BrandonBNguyen/Pitot-Static-Tube-Project/CAD/Teensy LC Model/Teensy_lc v8.png

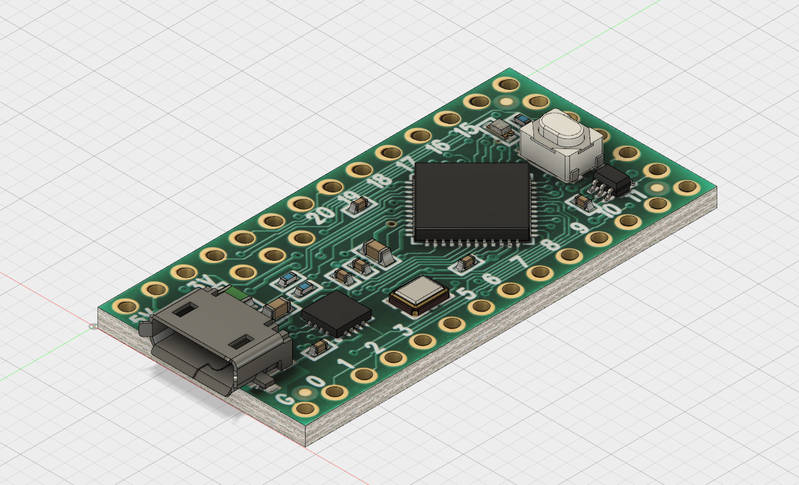
CAD/Teensy LC Model/Teensy_lc v8.png
