BrandonBNguyen/Pitot-Static-Tube-Project/CAD/Arduino Uno R3 Model/603 resistor.SLDPRT

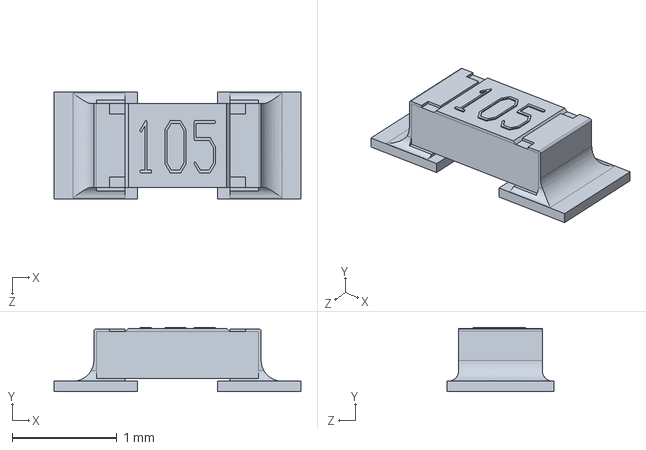
[picture p31: CAD file, 2021-01-14]
CAD/Arduino Uno R3 Model/603 resistor.SLDPRT
2.36 x 0.615 x 1.02 mm
