BrandonBNguyen/Pitot-Static-Tube-Project/CAD/Version 1/Pressure Sensor Housing.SLDPRT

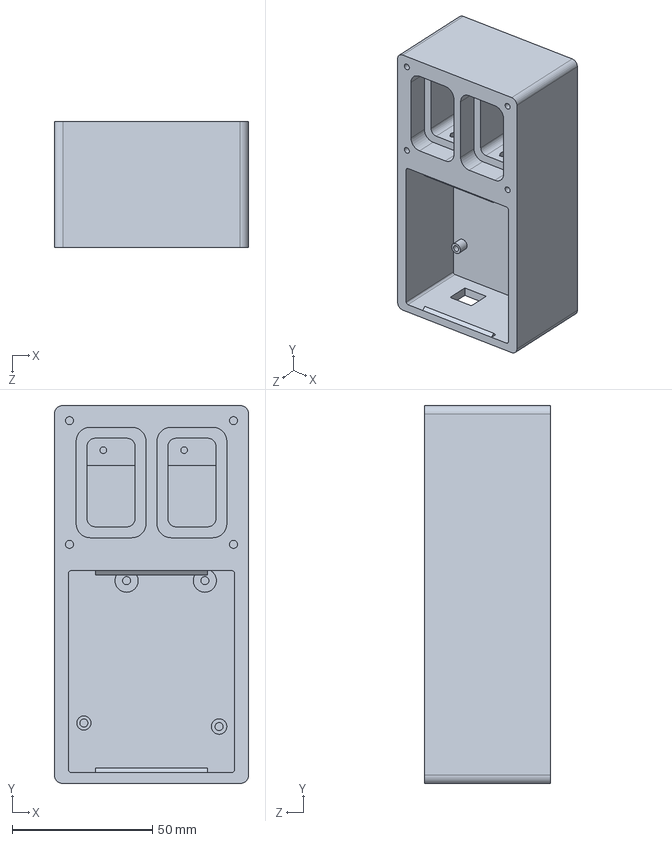
[picture p32: CAD file, 2021-02-09]
CAD/Version 1/Pressure Sensor Housing.SLDPRT
69.3 x 134.9 x 45.0 mm
