BrandonBNguyen/Pitot-Static-Tube-Project/Print STL Files/Pressure Sensor Housing Lid.STL

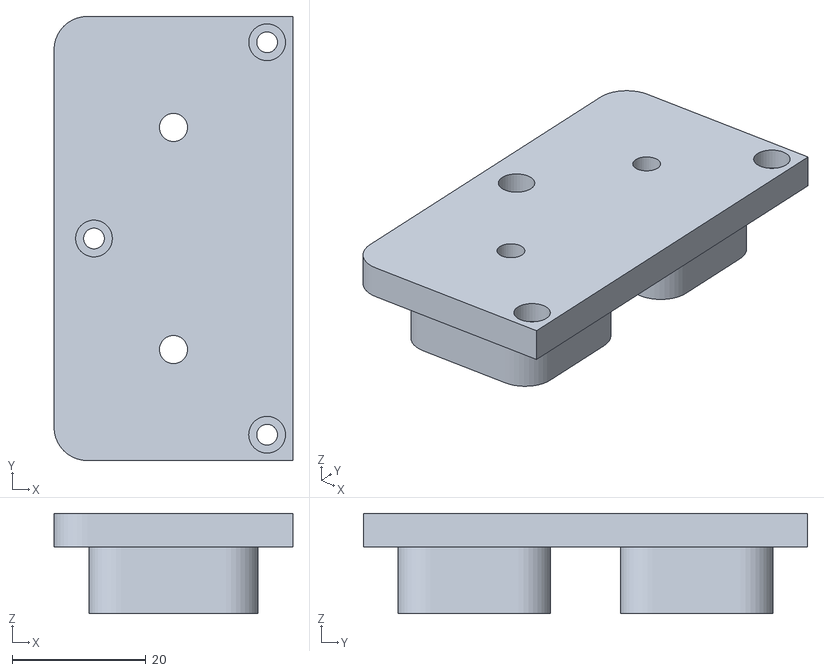
[picture p33: CAD file, 2021-02-09]
Print STL Files/Pressure Sensor Housing Lid.STL
35.7 x 66.4 x 15.0
