BrandonBNguyen/Pitot-Static-Tube-Project/Test Prints/Teensy LC Lid.STL

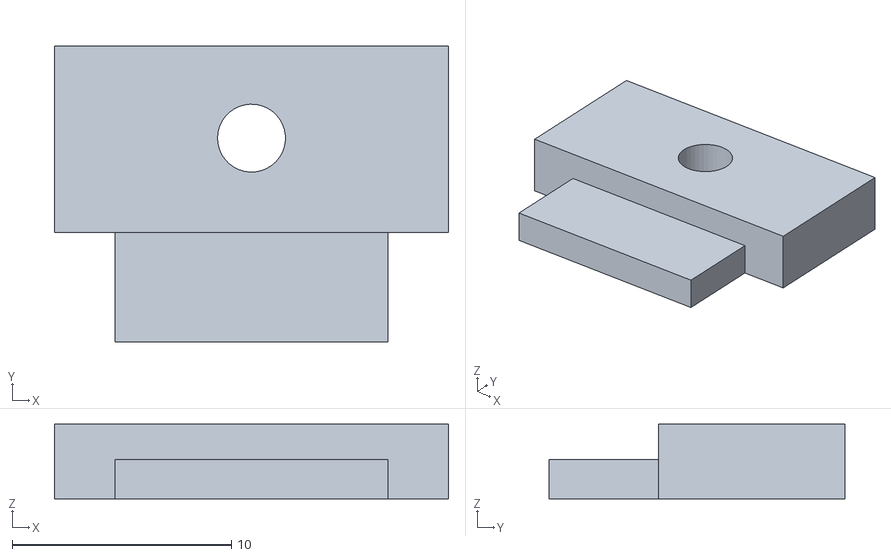
[picture p34: CAD file, 2021-02-09]
Test Prints/Teensy LC Lid.STL
18.0 x 13.5 x 3.40
