BrandonBNguyen/Pitot-Static-Tube-Project/CAD/Arduino Uno R3 Model/2pin_header__02.sldprt

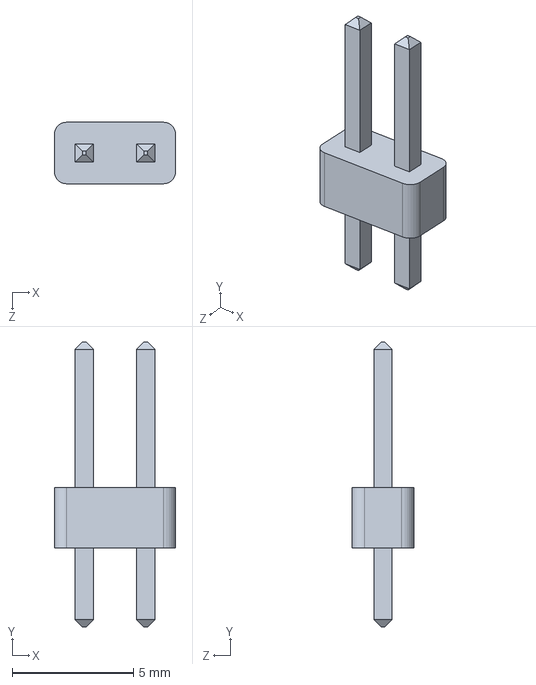
[picture p35: CAD file, 2021-01-14]
CAD/Arduino Uno R3 Model/2pin_header__02.sldprt
5.00 x 11.8 x 2.54 mm
