BrandonBNguyen/Pitot-Static-Tube-Project/Print STL Files/Teensy LC Fastener.STL

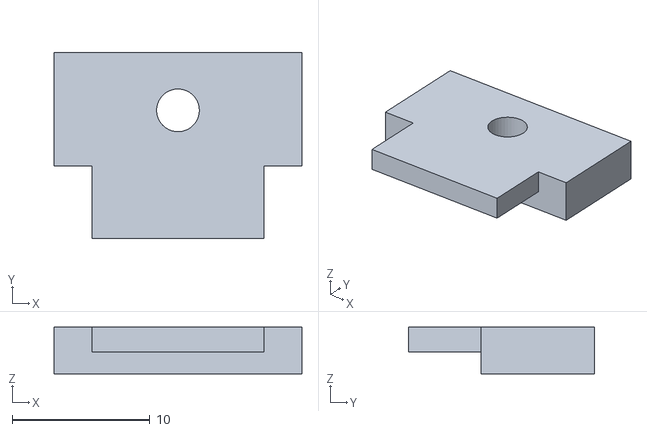
[picture p36: CAD file, 2021-02-09]
Print STL Files/Teensy LC Fastener.STL
18.0 x 13.5 x 3.40
