BrandonBNguyen/Pitot-Static-Tube-Project/Test Prints/BMP180 Housing.STL

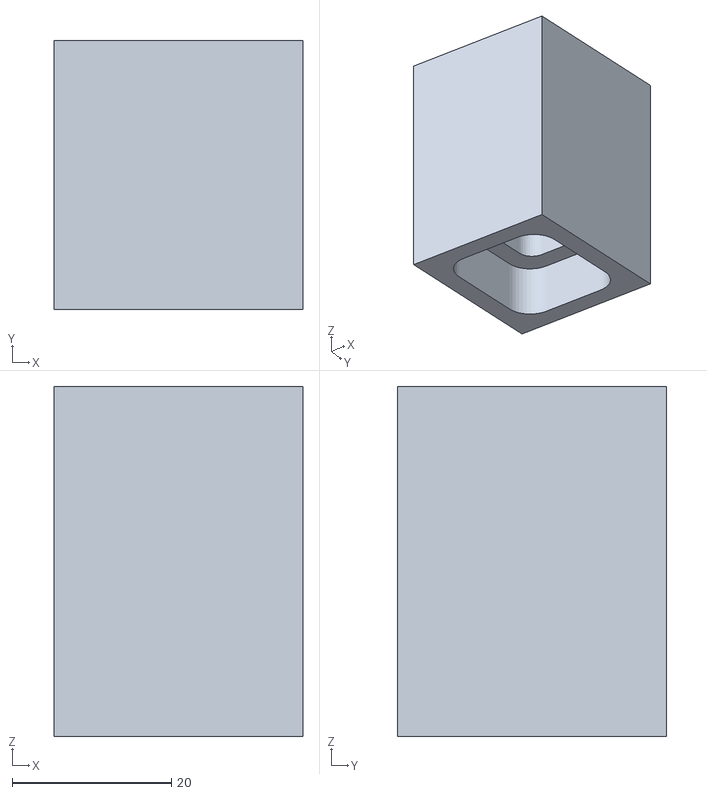
[picture p37: CAD file, 2021-02-09]
Test Prints/BMP180 Housing.STL
31.2 x 33.7 x 43.9
