BrandonBNguyen/Pitot-Static-Tube-Project/CAD/Arduino Uno R3 Model/ssot3.SLDPRT

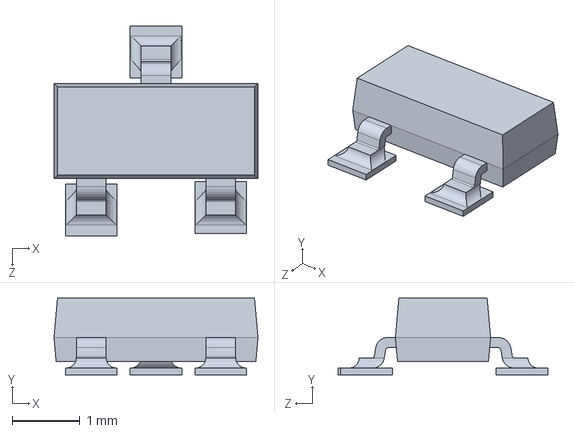
[picture p38: CAD file, 2021-01-14]
CAD/Arduino Uno R3 Model/ssot3.SLDPRT
3.00 x 1.13 x 3.09 mm
