BrandonBNguyen/Pitot-Static-Tube-Project/CAD/OLED-128x64-0.96.step

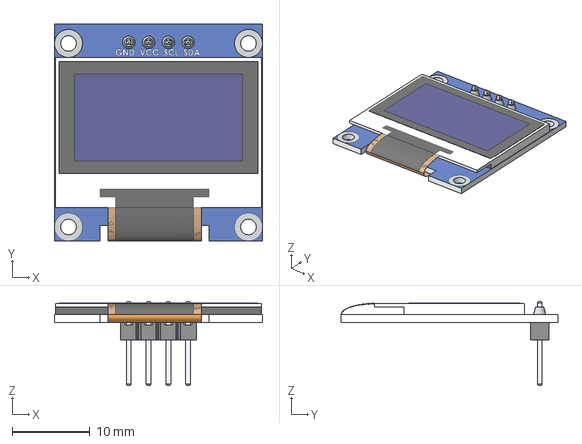
[picture p39: CAD file, 2021-02-09]
CAD/OLED-128x64-0.96.step
26.7 x 27.9 x 10.8 mm
