BrandonBNguyen/Pitot-Static-Tube-Project/Print STL Files/OLED Panel Holder.STL

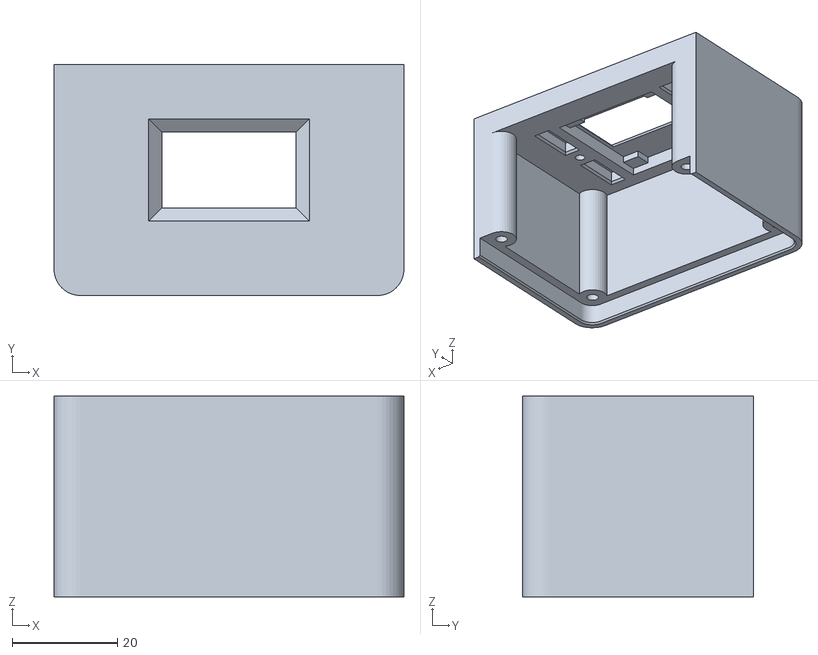
[picture p40: CAD file, 2021-02-09]
Print STL Files/OLED Panel Holder.STL
66.4 x 43.8 x 38.1
