BrandonBNguyen/Pitot-Static-Tube-Project/Test Prints/OLED Display Housing.STL

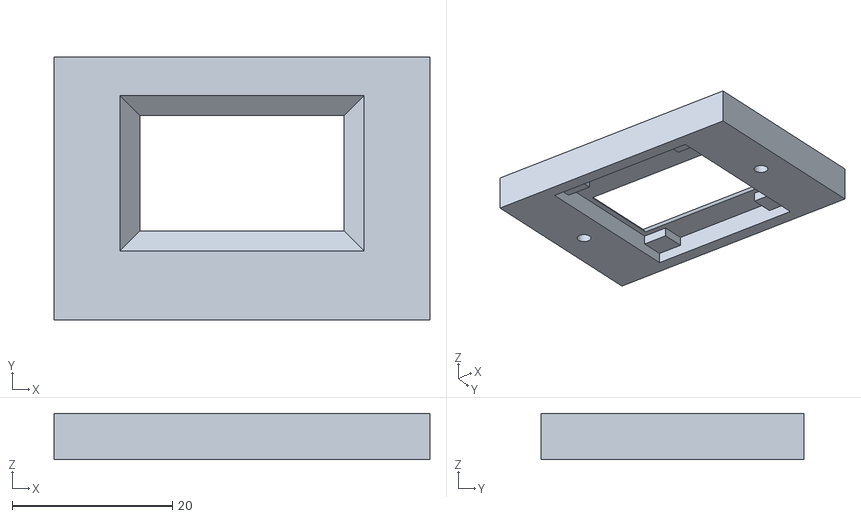
[picture p41: CAD file, 2021-02-09]
Test Prints/OLED Display Housing.STL
46.9 x 32.8 x 5.75
