BrandonBNguyen/Pitot-Static-Tube-Project/CAD/Arduino Uno R3 Model/lmv358.SLDPRT

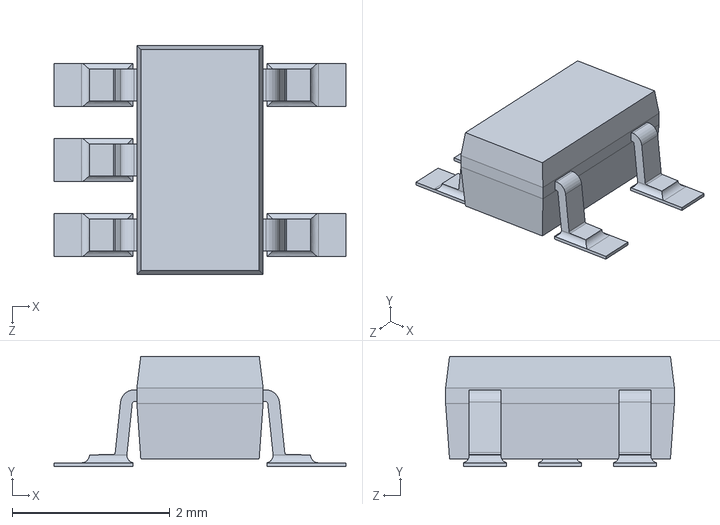
[picture p42: CAD file, 2021-01-14]
CAD/Arduino Uno R3 Model/lmv358.SLDPRT
3.70 x 1.40 x 2.90 mm
