BrandonBNguyen/Pitot-Static-Tube-Project/CAD/Pin Connector.SLDPRT

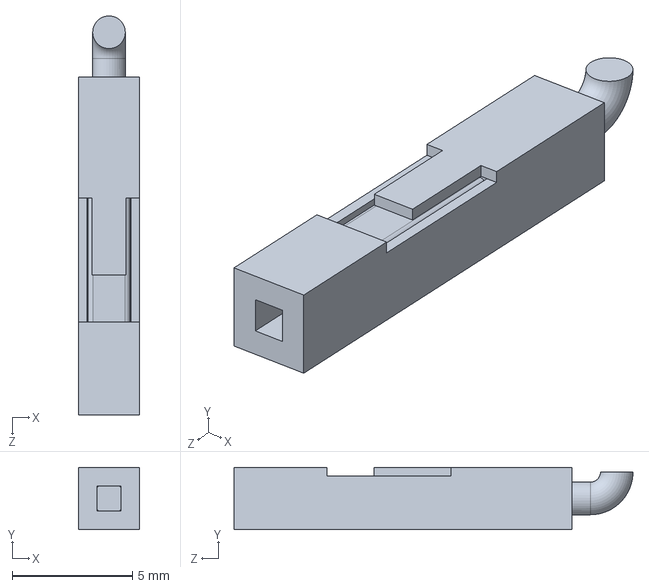
[picture p43: CAD file, 2021-02-09]
CAD/Pin Connector.SLDPRT
2.55 x 2.60 x 16.6 mm
