BrandonBNguyen/Pitot-Static-Tube-Project/Print STL Files/Pressure Sensor Housing.STL

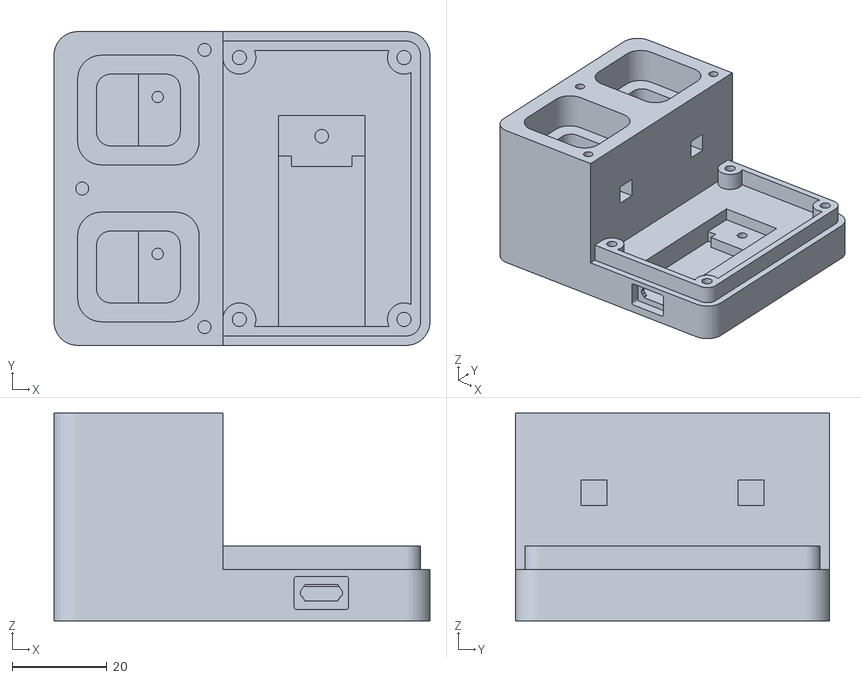
[picture p44: CAD file, 2021-02-09]
Print STL Files/Pressure Sensor Housing.STL
79.6 x 66.4 x 43.9
