BrandonBNguyen/Pitot-Static-Tube-Project/Test Prints/OLED Display Fastener.STL

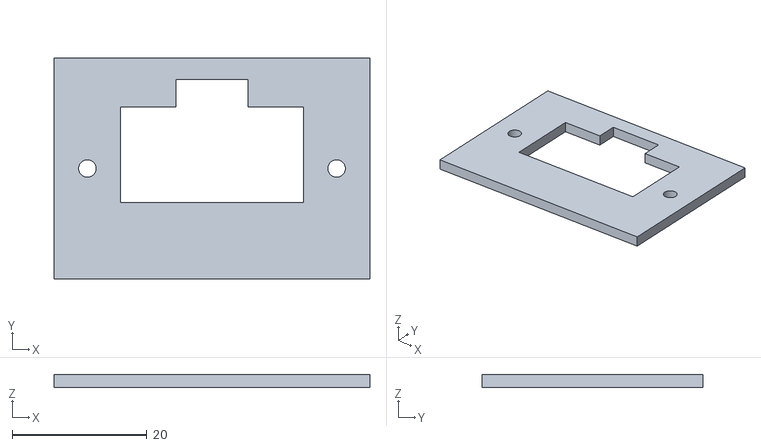
[picture p45: CAD file, 2021-02-09]
Test Prints/OLED Display Fastener.STL
46.9 x 32.8 x 2.00
