BrandonBNguyen/Pitot-Static-Tube-Project/CAD/Arduino Uno R3 Model/blm21.SLDPRT

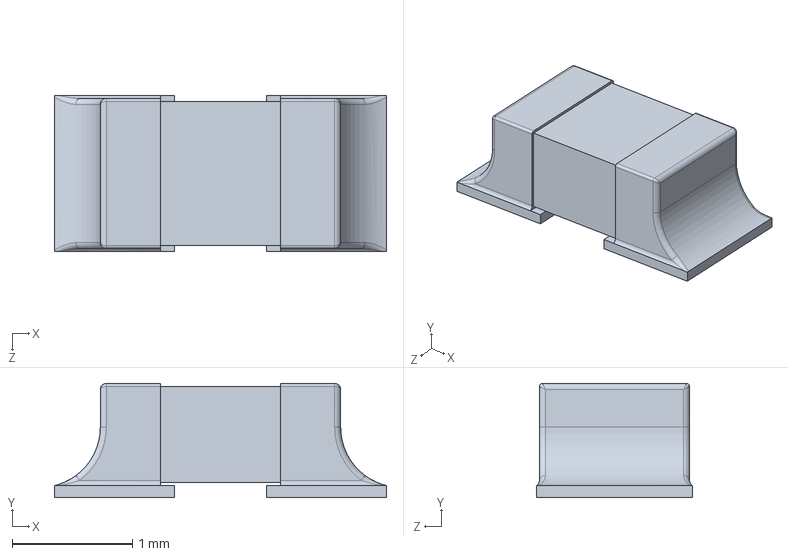
[picture p46: CAD file, 2021-01-14]
CAD/Arduino Uno R3 Model/blm21.SLDPRT
2.76 x 0.95 x 1.30 mm
