BrandonBNguyen/Pitot-Static-Tube-Project/CAD/Pin Connector Male.SLDPRT

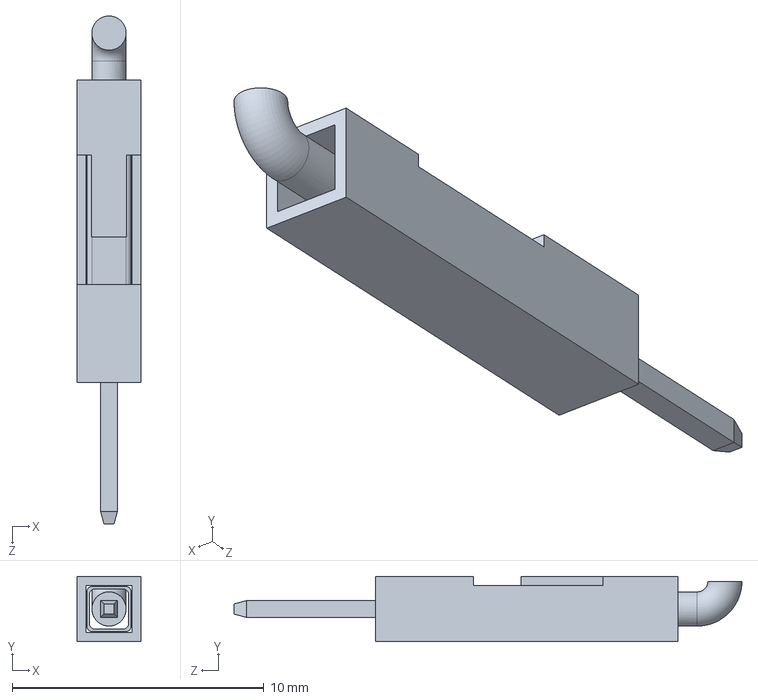
[picture p47: CAD file, 2021-01-15]
CAD/Pin Connector Male.SLDPRT
2.55 x 2.60 x 20.2 mm
