BrandonBNguyen/Pitot-Static-Tube-Project/Print STL Files/Nozzle Support.STL

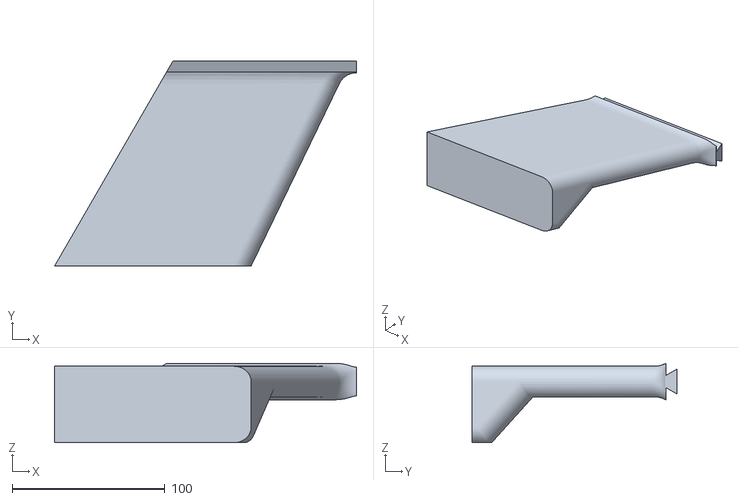
[picture p48: CAD file, 2021-01-28]
Print STL Files/Nozzle Support.STL
197.5 x 134.2 x 51.9
