BrandonBNguyen/Pitot-Static-Tube-Project/CAD/Arduino Uno R3 Model/lp2985dgkr.SLDPRT

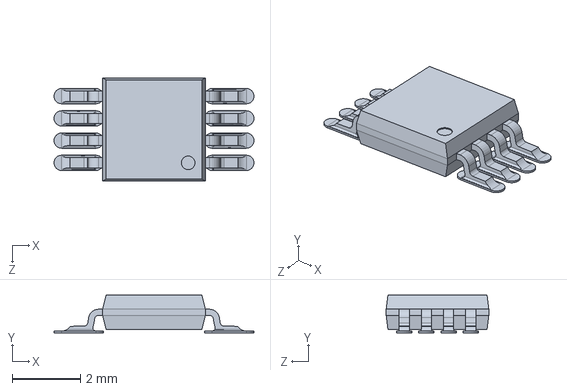
[picture p49: CAD file, 2021-01-14]
CAD/Arduino Uno R3 Model/lp2985dgkr.SLDPRT
5.85 x 1.10 x 3.00 mm
