BrandonBNguyen/Pitot-Static-Tube-Project/CAD/bmp180.SLDPRT

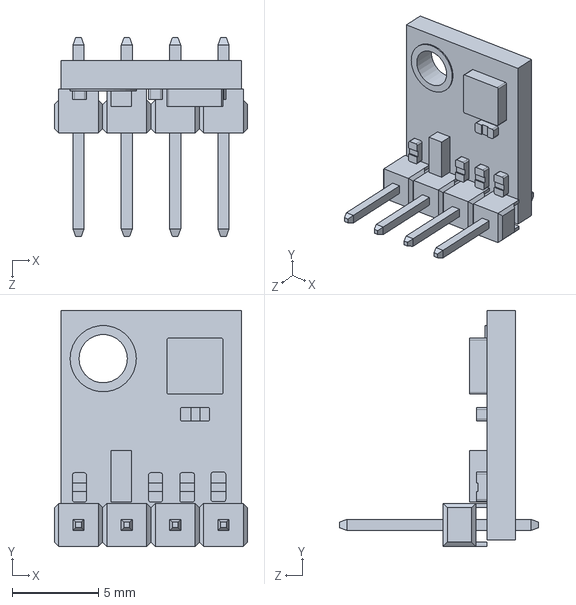
[picture p50: CAD file, 2021-01-15]
CAD/bmp180.SLDPRT
11.2 x 13.7 x 11.5 mm
