BrandonBNguyen/Pitot-Static-Tube-Project/Print STL Files/Nozzle.STL

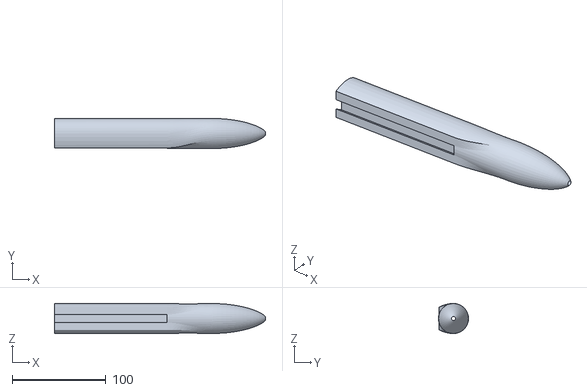
[picture p51: CAD file, 2021-01-28]
Print STL Files/Nozzle.STL
224.9 x 32.0 x 32.0
