BrandonBNguyen/Pitot-Static-Tube-Project/CAD/Arduino Uno R3 Model/RESET.SLDPRT

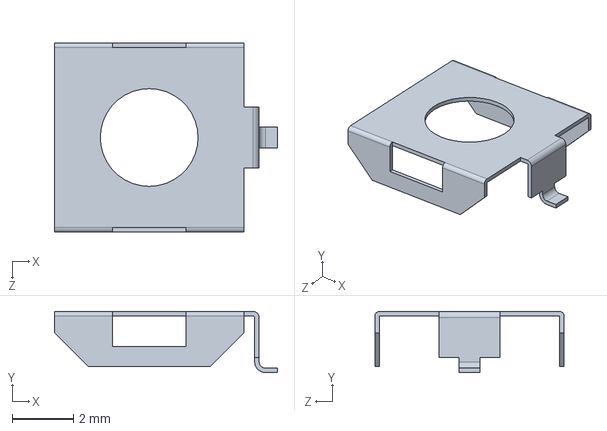
[picture p52: CAD file, 2021-01-14]
CAD/Arduino Uno R3 Model/RESET.SLDPRT
7.30 x 2.00 x 6.20 mm
