BrandonBNguyen/Pitot-Static-Tube-Project/CAD/Arduino Uno R3 Model/cd1206 diode.SLDPRT

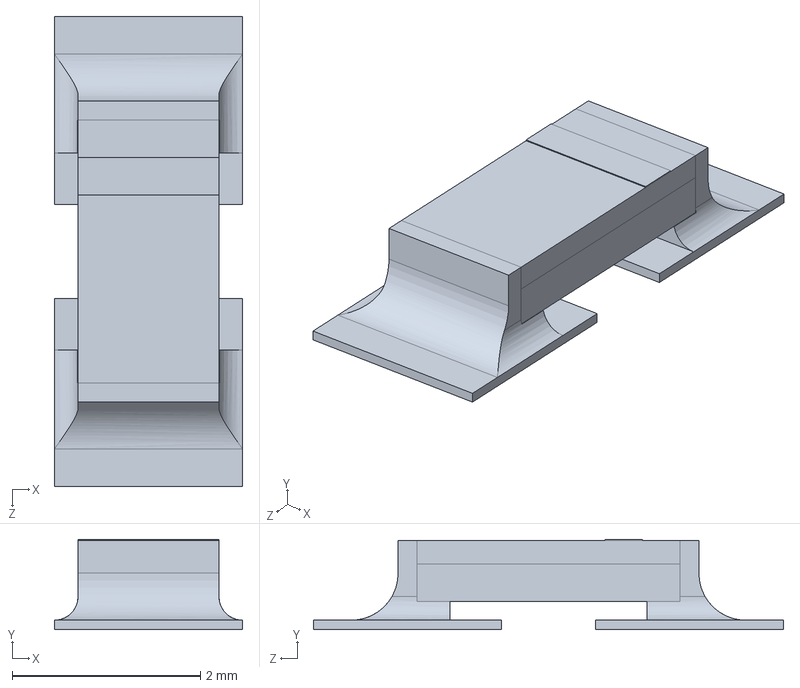
[picture p53: CAD file, 2021-01-14]
CAD/Arduino Uno R3 Model/cd1206 diode.SLDPRT
2.00 x 0.96 x 5.00 mm
