BrandonBNguyen/Pitot-Static-Tube-Project/CAD/Arduino Uno R3 Model/USB core.SLDPRT

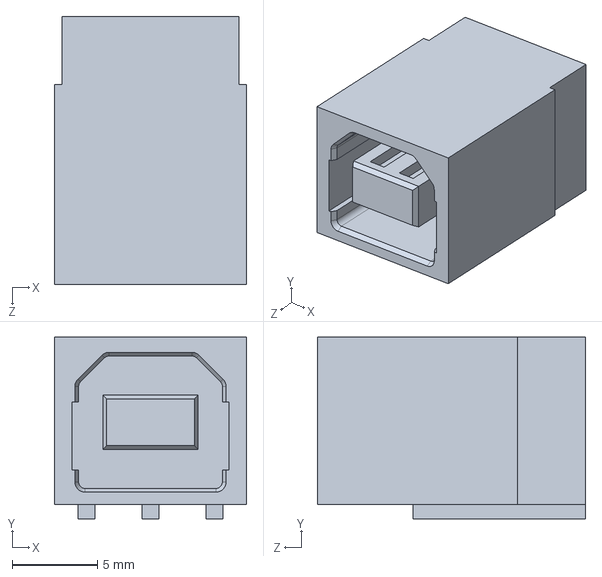
[picture p54: CAD file, 2021-01-14]
CAD/Arduino Uno R3 Model/USB core.SLDPRT
11.3 x 10.7 x 15.8 mm
