BrandonBNguyen/Pitot-Static-Tube-Project/CAD/Arduino Uno R3 Model/PADS001.SLDPRT

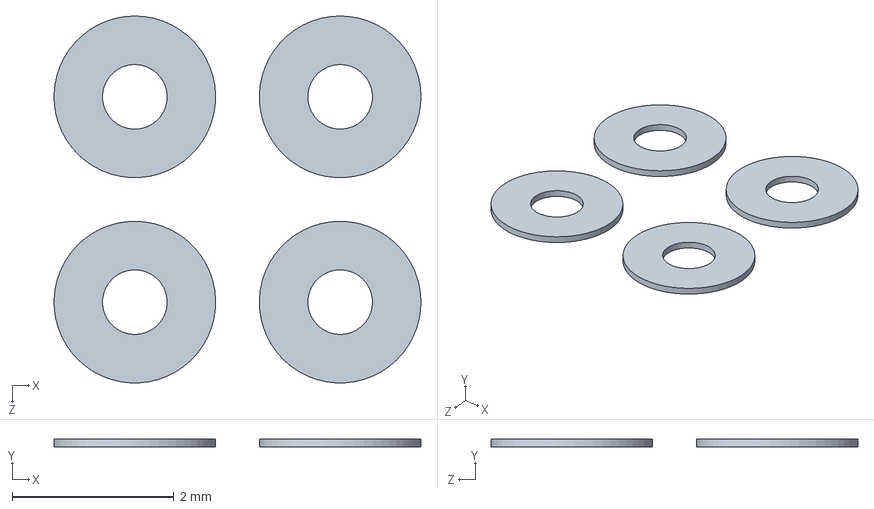
[picture p55: CAD file, 2021-01-14]
CAD/Arduino Uno R3 Model/PADS001.SLDPRT
4.54 x 0.1 x 4.54 mm
