BrandonBNguyen/Pitot-Static-Tube-Project/CAD/Arduino Uno R3 Model/crystal.sldprt

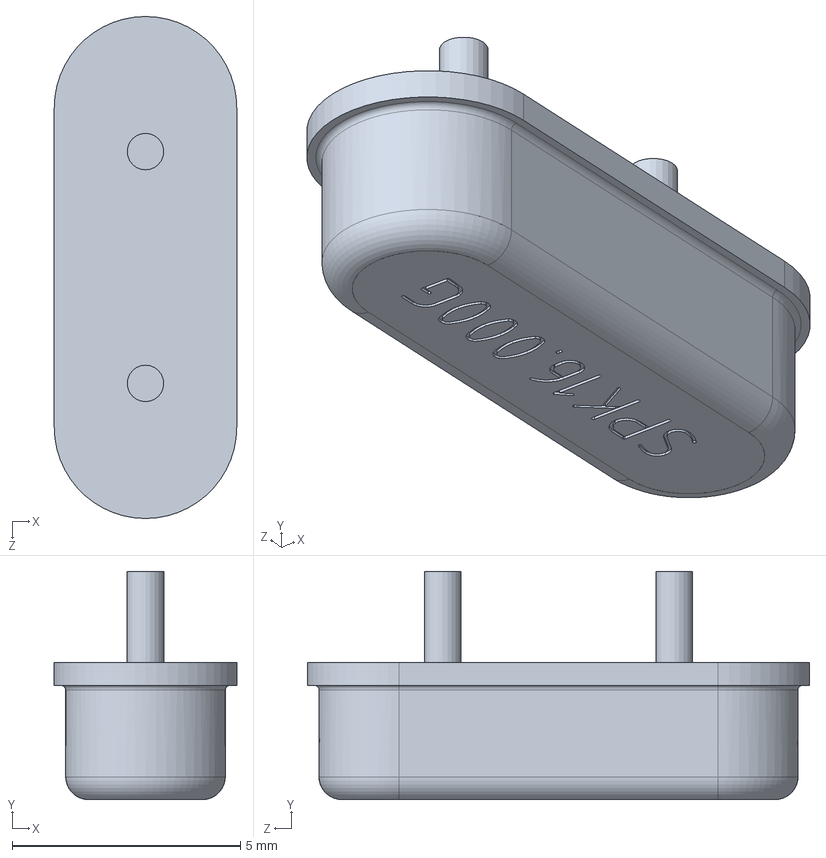
[picture p56: CAD file, 2021-01-14]
CAD/Arduino Uno R3 Model/crystal.sldprt
4.00 x 5.00 x 11.0 mm
