BrandonBNguyen/Pitot-Static-Tube-Project/CAD/Arduino Uno R3 Model/603 cap on pad.SLDPRT

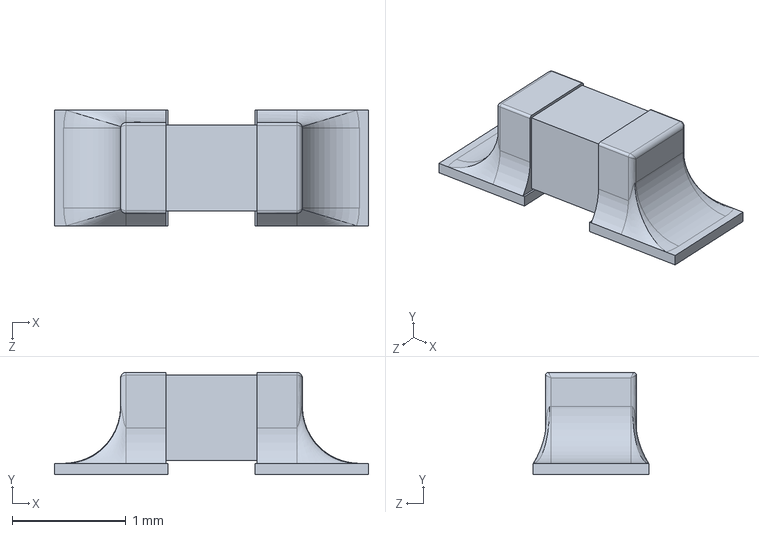
[picture p57: CAD file, 2021-01-14]
CAD/Arduino Uno R3 Model/603 cap on pad.SLDPRT
2.76 x 0.9 x 1.02 mm
