BrandonBNguyen/Pitot-Static-Tube-Project/CAD/Arduino Uno R3 Model/MLC0603.SLDPRT

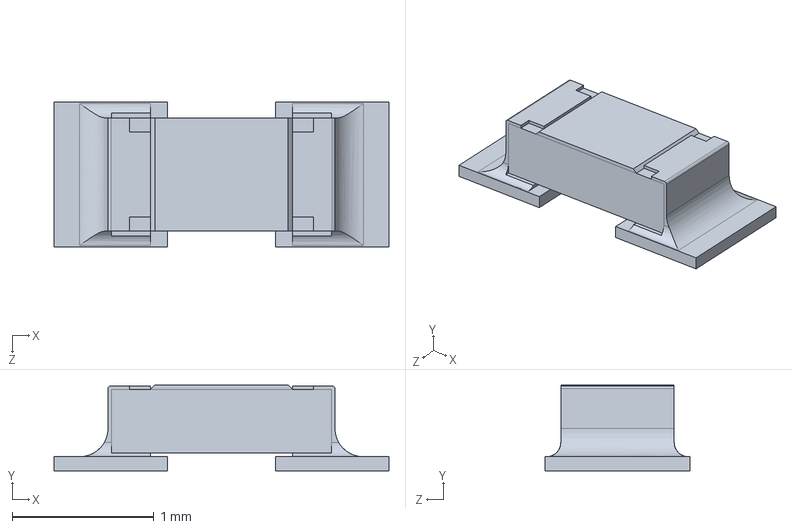
[picture p58: CAD file, 2021-01-14]
CAD/Arduino Uno R3 Model/MLC0603.SLDPRT
2.36 x 0.605 x 1.02 mm
