BrandonBNguyen/Pitot-Static-Tube-Project/CAD/Arduino Uno R3 Model/47uf CAP Dcase.SLDPRT

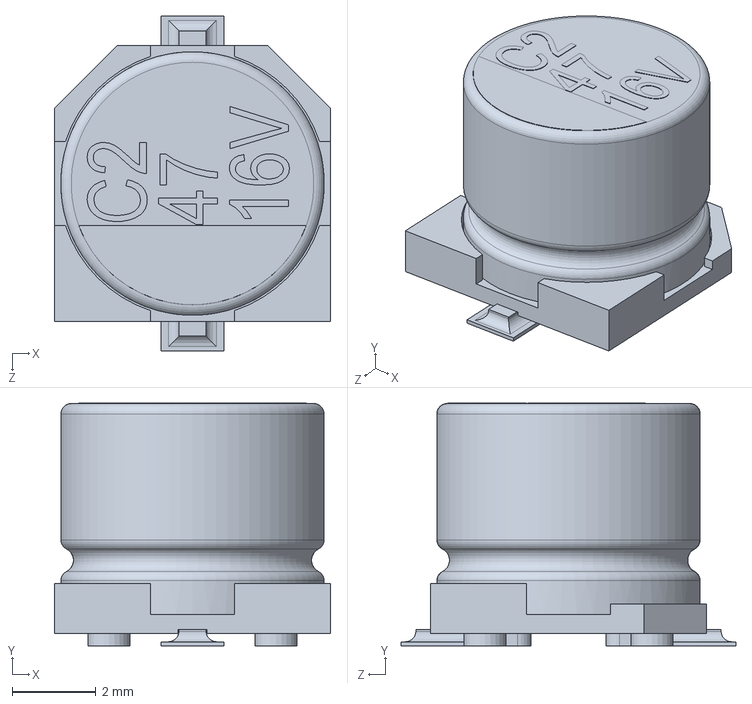
[picture p59: CAD file, 2021-01-14]
CAD/Arduino Uno R3 Model/47uf CAP Dcase.SLDPRT
6.60 x 5.81 x 8.00 mm
