BrandonBNguyen/Pitot-Static-Tube-Project/CAD/Arduino Uno R3 Model/ATMEL328P.SLDPRT

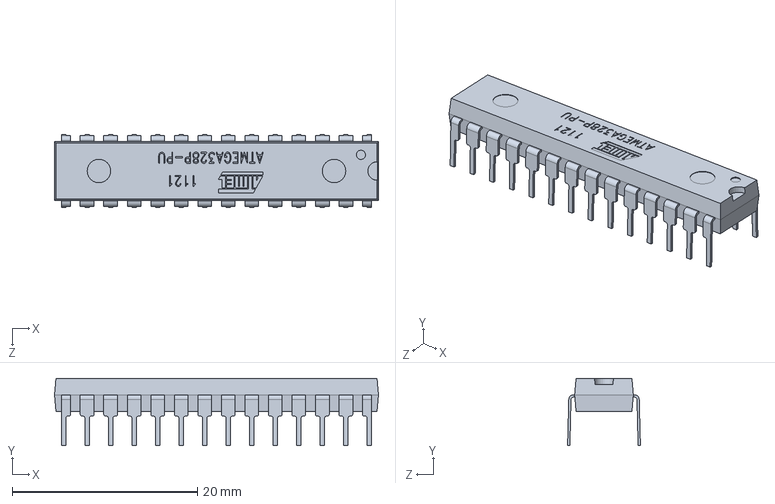
[picture p60: CAD file, 2021-01-14]
CAD/Arduino Uno R3 Model/ATMEL328P.SLDPRT
35.0 x 7.27 x 7.87 mm
