BrandonBNguyen/Pitot-Static-Tube-Project/CAD/Arduino Uno R3 Model/led.SLDPRT

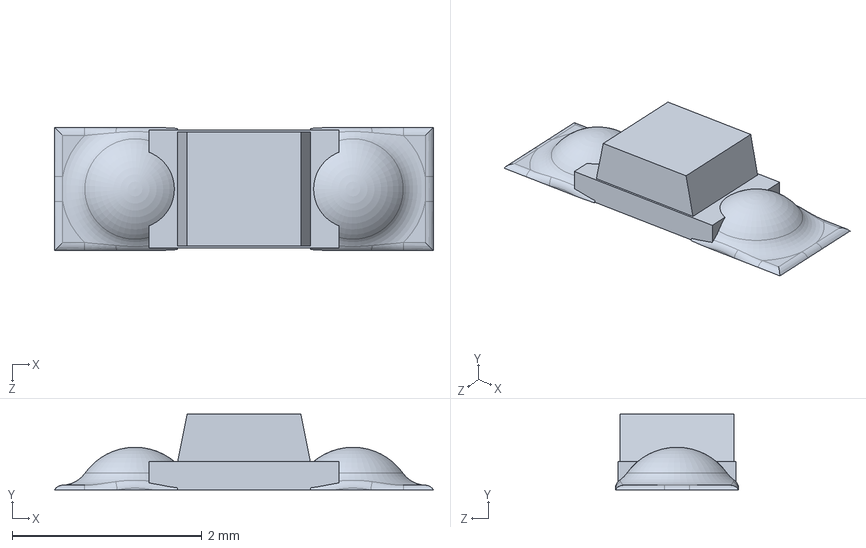
[picture p61: CAD file, 2021-01-14]
CAD/Arduino Uno R3 Model/led.SLDPRT
4.00 x 0.8 x 1.30 mm
