BrandonBNguyen/Pitot-Static-Tube-Project/CAD/Arduino Uno R3 Model/atmega16u2.SLDPRT

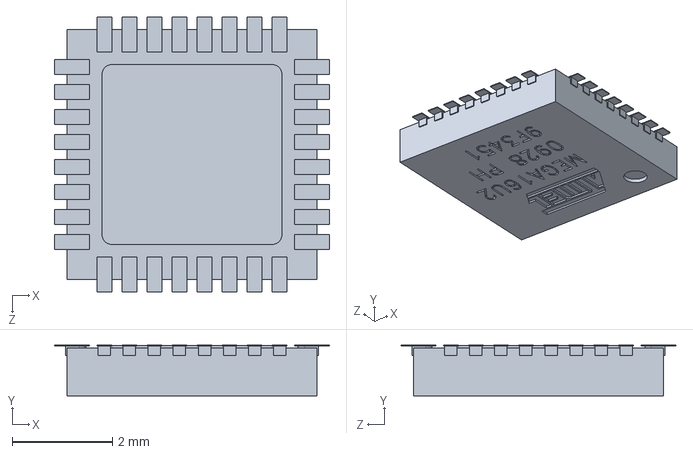
[picture p62: CAD file, 2021-01-14]
CAD/Arduino Uno R3 Model/atmega16u2.SLDPRT
5.50 x 1.01 x 5.50 mm
