BrandonBNguyen/Pitot-Static-Tube-Project/CAD/Arduino Uno R3 Model/10 PORT HEADER.SLDPRT

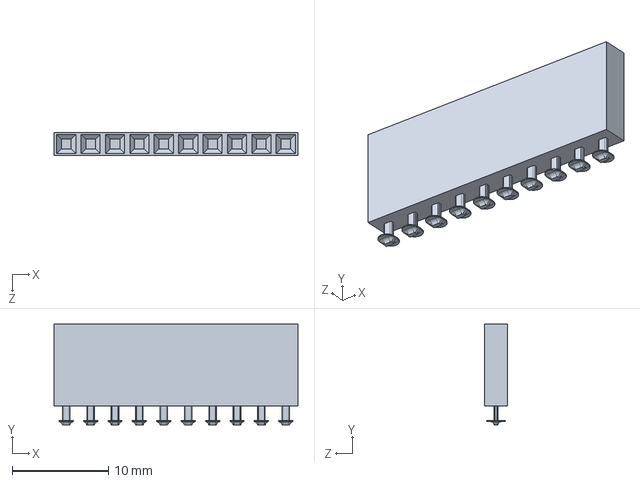
[picture p63: CAD file, 2021-01-14]
CAD/Arduino Uno R3 Model/10 PORT HEADER.SLDPRT
25.4 x 10.5 x 2.41 mm
