BrandonBNguyen/Pitot-Static-Tube-Project/CAD/Arduino Uno R3 Model/dip socket pin.SLDPRT

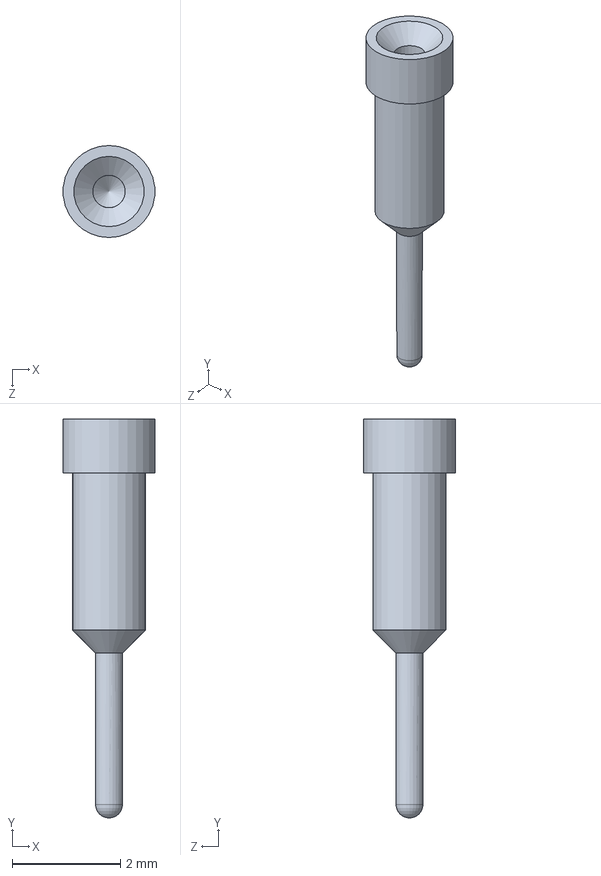
[picture p64: CAD file, 2021-01-14]
CAD/Arduino Uno R3 Model/dip socket pin.SLDPRT
1.69 x 7.37 x 1.70 mm
