BrandonBNguyen/Pitot-Static-Tube-Project/CAD/Arduino Uno R3 Model/USB SHELL.SLDPRT

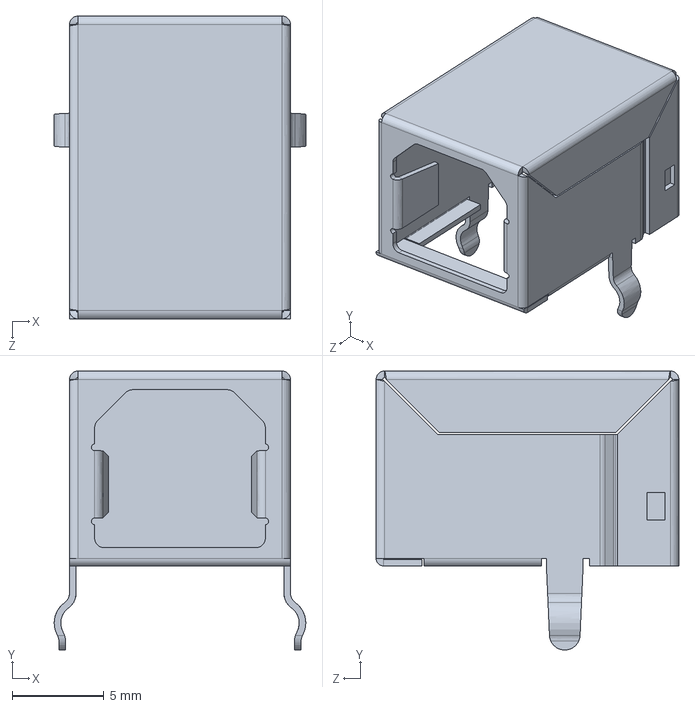
[picture p65: CAD file, 2021-01-14]
CAD/Arduino Uno R3 Model/USB SHELL.SLDPRT
13.7 x 15.2 x 16.5 mm
