BrandonBNguyen/Pitot-Static-Tube-Project/CAD/Arduino Uno R3 Model/16mhz crystal - measured.SLDPRT

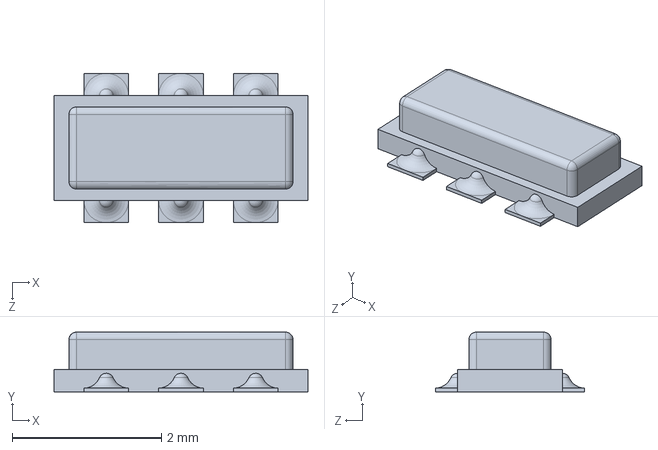
[picture p66: CAD file, 2021-01-14]
CAD/Arduino Uno R3 Model/16mhz crystal - measured.SLDPRT
3.40 x 0.8 x 2.00 mm
