BrandonBNguyen/Pitot-Static-Tube-Project/CAD/Arduino Uno R3 Model/usb top contact.SLDPRT

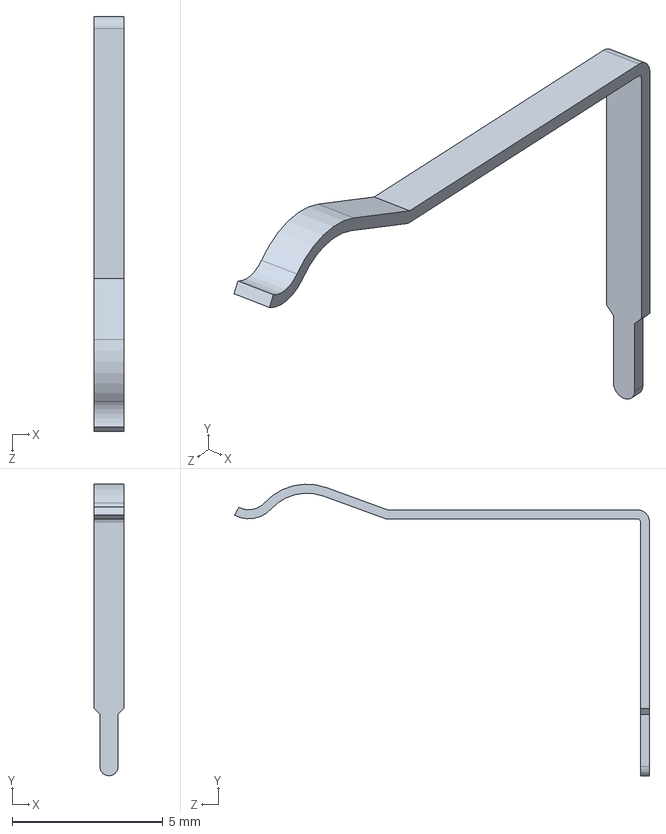
[picture p67: CAD file, 2021-01-14]
CAD/Arduino Uno R3 Model/usb top contact.SLDPRT
1.00 x 9.67 x 13.8 mm
