BrandonBNguyen/Pitot-Static-Tube-Project/CAD/Arduino Uno R3 Model/usb btm contact.SLDPRT

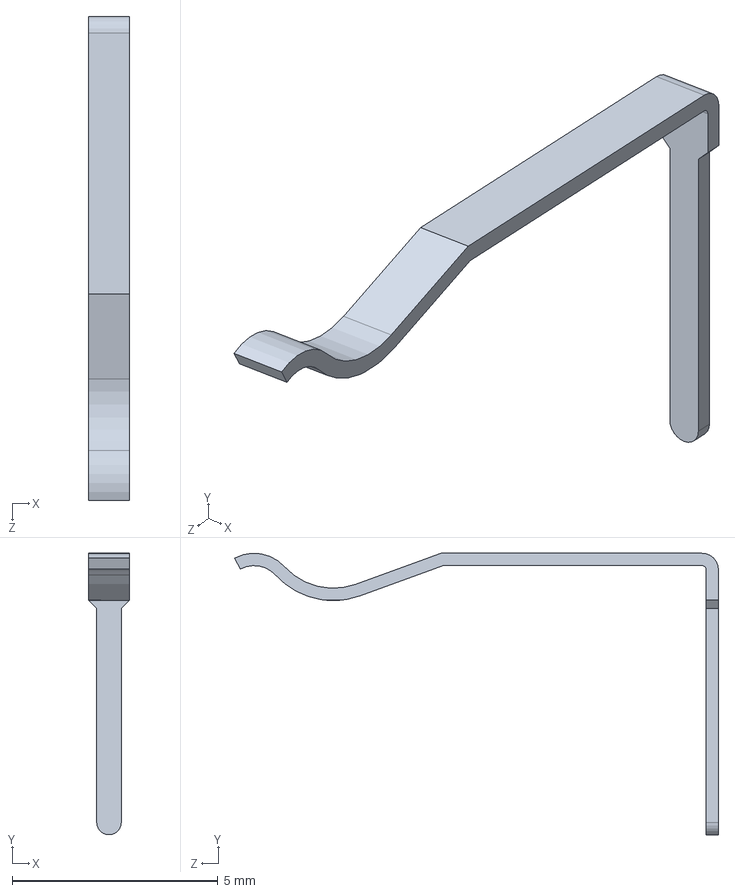
[picture p68: CAD file, 2021-01-14]
CAD/Arduino Uno R3 Model/usb btm contact.SLDPRT
1.00 x 6.84 x 11.8 mm
