BrandonBNguyen/Pitot-Static-Tube-Project/CAD/Arduino Uno R3 Model/unoboard blue.SLDPRT

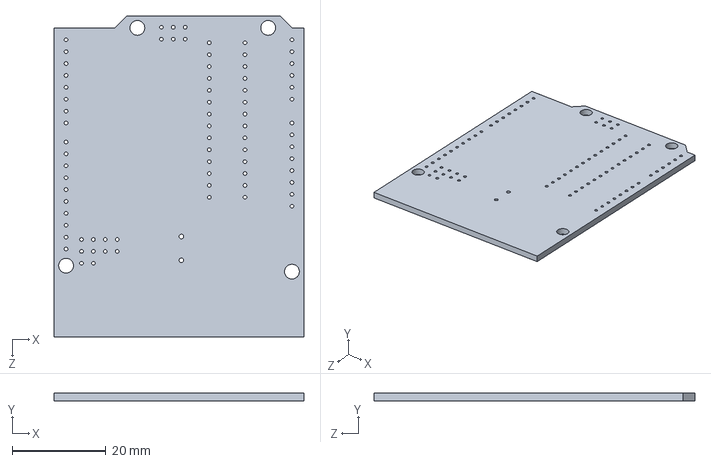
[picture p69: CAD file, 2021-01-14]
CAD/Arduino Uno R3 Model/unoboard blue.SLDPRT
53.3 x 1.65 x 68.6 mm
