BrandonBNguyen/Pitot-Static-Tube-Project/CAD/Arduino Uno R3 Model/power jack.SLDPRT

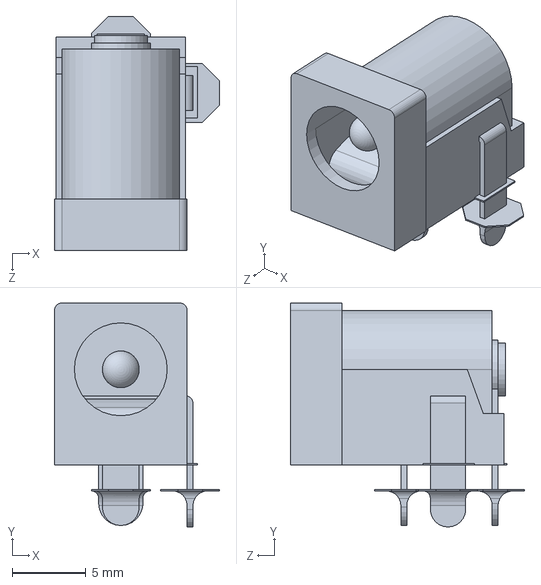
[picture p70: CAD file, 2021-01-14]
CAD/Arduino Uno R3 Model/power jack.SLDPRT
11.2 x 15.2 x 15.9 mm
