BrandonBNguyen/Pitot-Static-Tube-Project/CAD/Arduino Uno R3 Model/m7 diode.SLDPRT

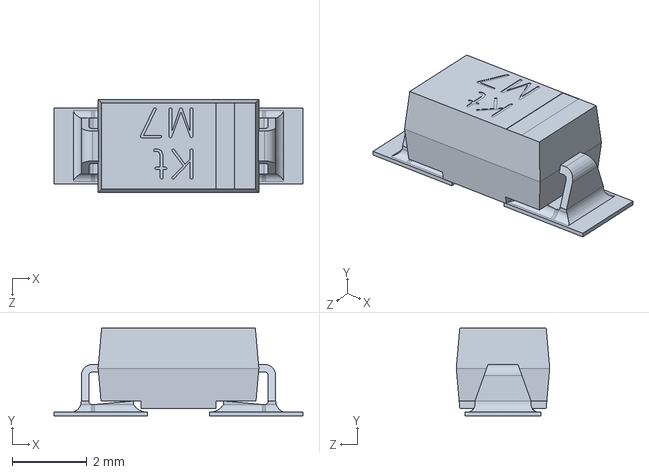
[picture p71: CAD file, 2021-01-14]
CAD/Arduino Uno R3 Model/m7 diode.SLDPRT
6.66 x 2.35 x 2.50 mm
