BrandonBNguyen/Pitot-Static-Tube-Project/CAD/Arduino Uno R3 Model/nano - reg.SLDPRT

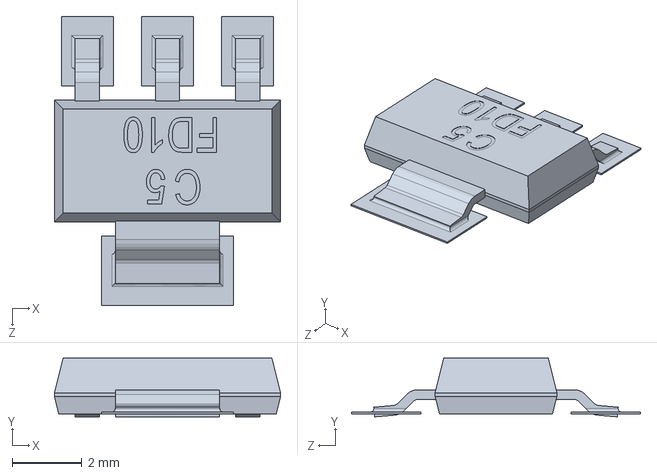
[picture p72: CAD file, 2021-01-14]
CAD/Arduino Uno R3 Model/nano - reg.SLDPRT
6.50 x 1.69 x 8.30 mm
