BrandonBNguyen/Pitot-Static-Tube-Project/CAD/Arduino Uno R3 Model/mf-msmf050-2.SLDPRT

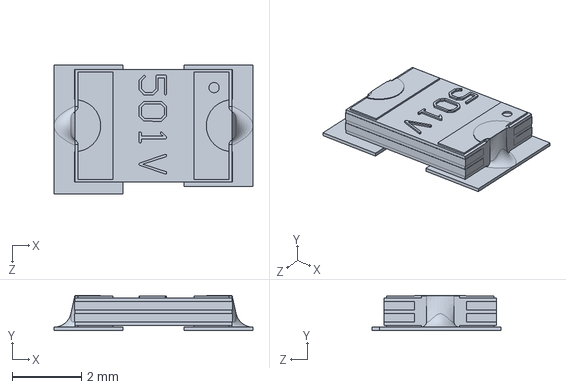
[picture p73: CAD file, 2021-01-14]
CAD/Arduino Uno R3 Model/mf-msmf050-2.SLDPRT
5.75 x 1.02 x 3.72 mm
