BrandonBNguyen/Pitot-Static-Tube-Project/CAD/Arduino Uno R3 Model/RESET CORE.SLDPRT

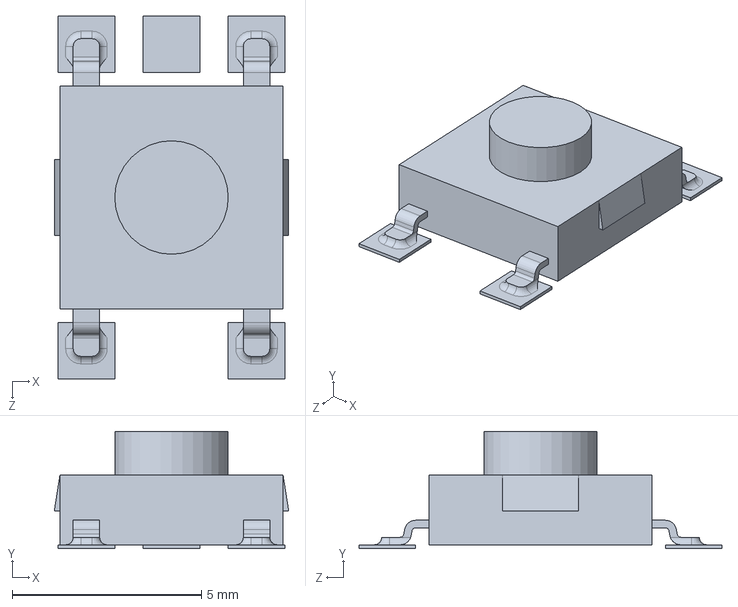
[picture p74: CAD file, 2021-01-14]
CAD/Arduino Uno R3 Model/RESET CORE.SLDPRT
6.20 x 3.10 x 9.60 mm
