BrandonBNguyen/Pitot-Static-Tube-Project/CAD/Arduino Uno R3 Model/6 PORT HEADER.SLDPRT

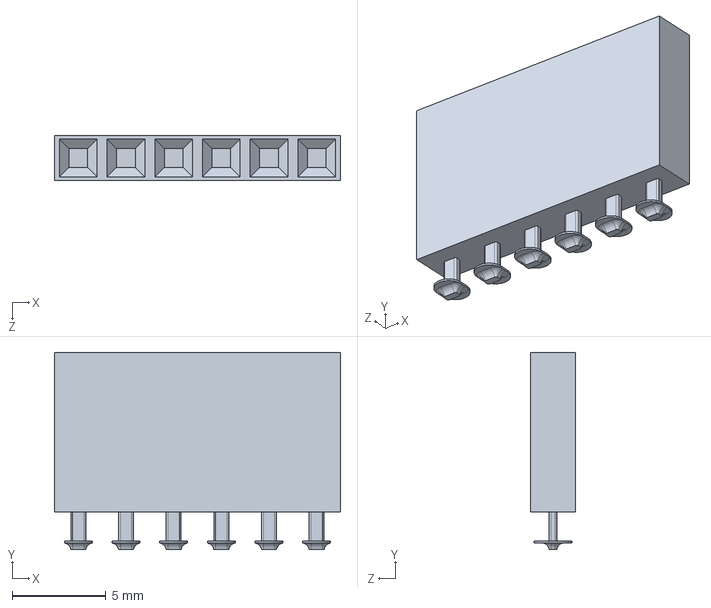
[picture p75: CAD file, 2021-01-14]
CAD/Arduino Uno R3 Model/6 PORT HEADER.SLDPRT
15.2 x 10.5 x 2.41 mm
