BrandonBNguyen/Pitot-Static-Tube-Project/CAD/Arduino Uno R3 Model/8 PORT HEADER.SLDPRT

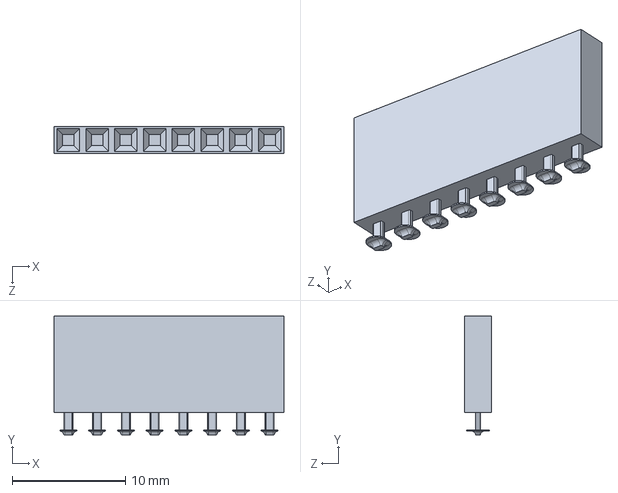
[picture p76: CAD file, 2021-01-14]
CAD/Arduino Uno R3 Model/8 PORT HEADER.SLDPRT
20.3 x 10.5 x 2.41 mm
